dragon-mobile/we_ssr_control/docs/1670702063162.jpg

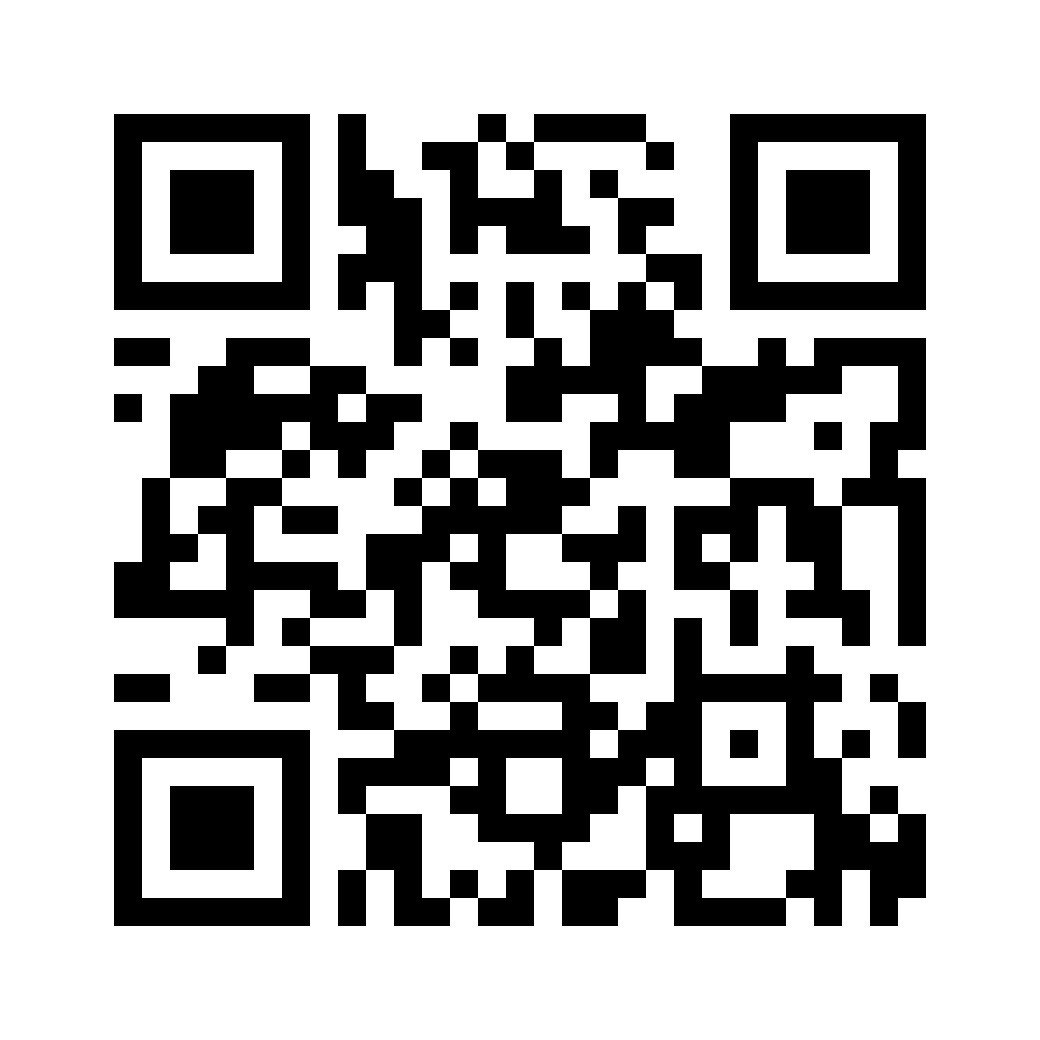
docs/1670702063162.jpg
